yashveerjain/Manipulative-Wheeled-Robot-for-Hospitality-Industry/robo_details/ArmLink1.PNG

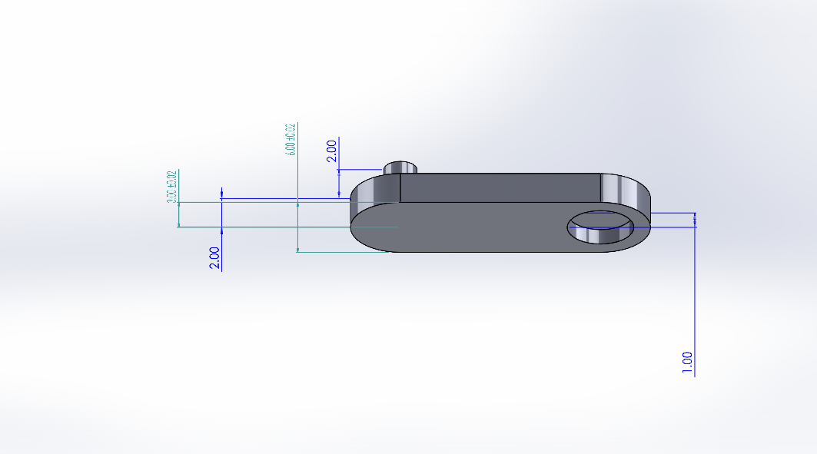
robo_details/ArmLink1.PNG
