yashveerjain/Manipulative-Wheeled-Robot-for-Hospitality-Industry/robo_details/end-effector.PNG

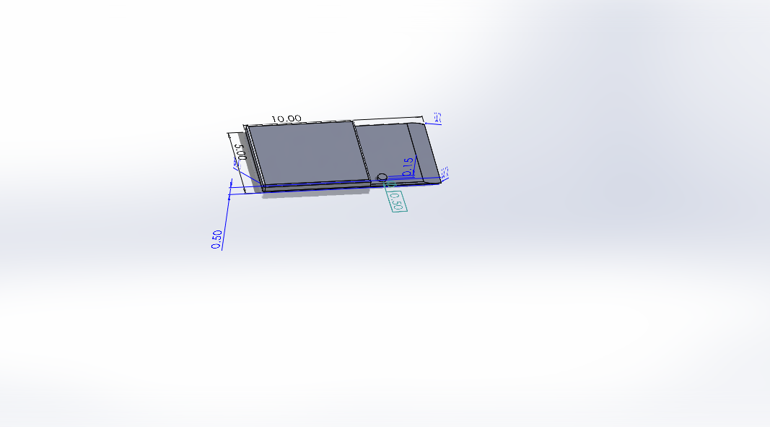
robo_details/end-effector.PNG
