yashveerjain/Manipulative-Wheeled-Robot-for-Hospitality-Industry/robo_details/robot-base.PNG

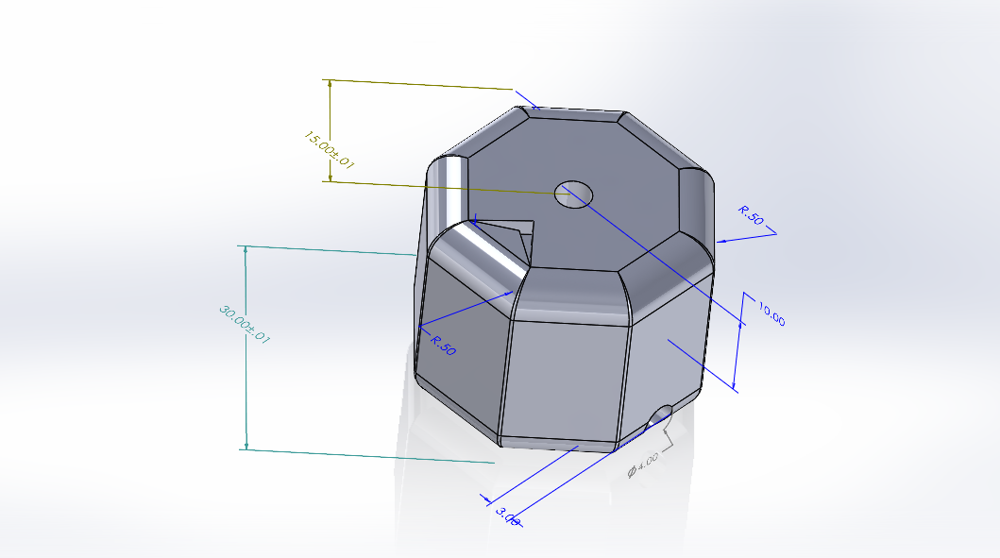
robo_details/robot-base.PNG
