yashveerjain/Manipulative-Wheeled-Robot-for-Hospitality-Industry/robot_part_files_solidworks/Link1-2Link2Joint.SLDPRT

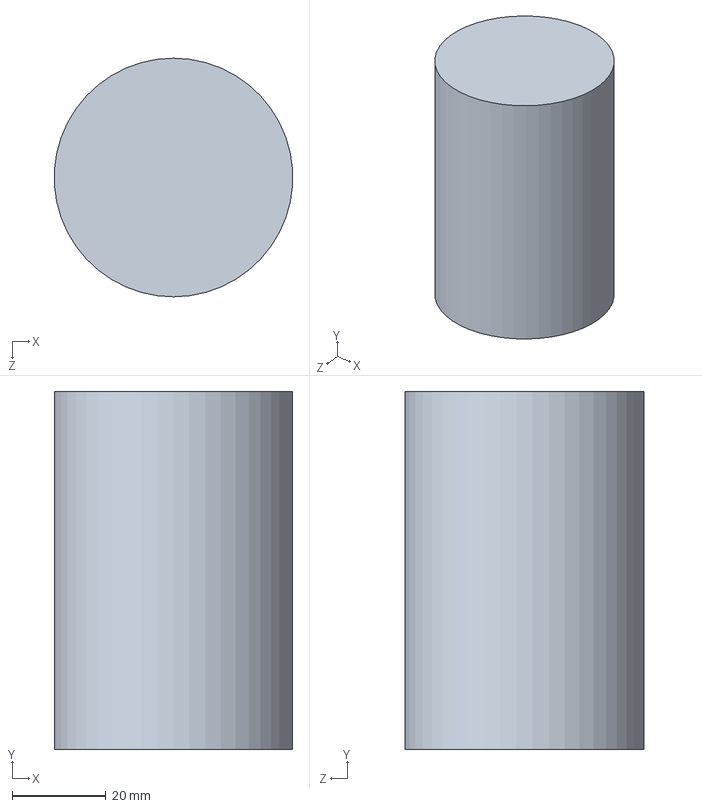
[picture p34: CAD file, 2022-12-05]
robot_part_files_solidworks/Link1-2Link2Joint.SLDPRT
50.7 x 76.2 x 50.8 mm
