yashveerjain/Manipulative-Wheeled-Robot-for-Hospitality-Industry/robot_part_files_solidworks/Base2Link1Joint.SLDPRT

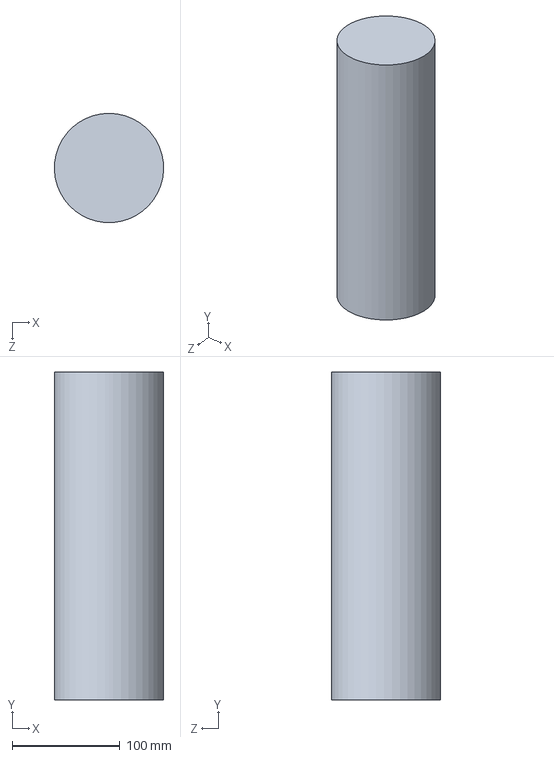
[picture p35: CAD file, 2022-12-05]
robot_part_files_solidworks/Base2Link1Joint.SLDPRT
101.5 x 304.8 x 101.6 mm
