yashveerjain/Manipulative-Wheeled-Robot-for-Hospitality-Industry/robo_details/RobotAssembly.PNG

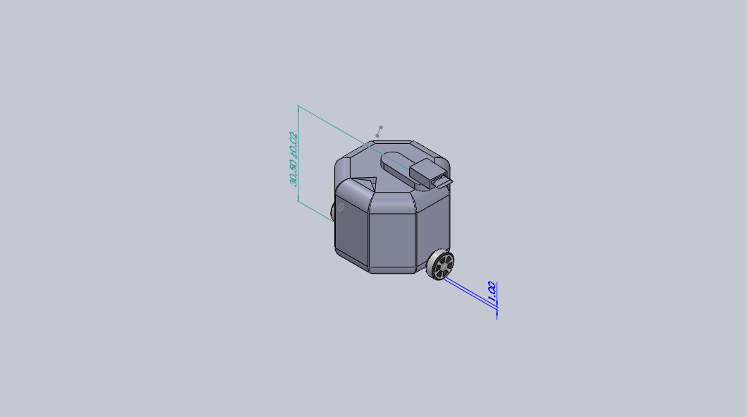
robo_details/RobotAssembly.PNG
